johnnyhuy/s2000-digital-dash/docs/assets/compare/compare_ap2_caution.png

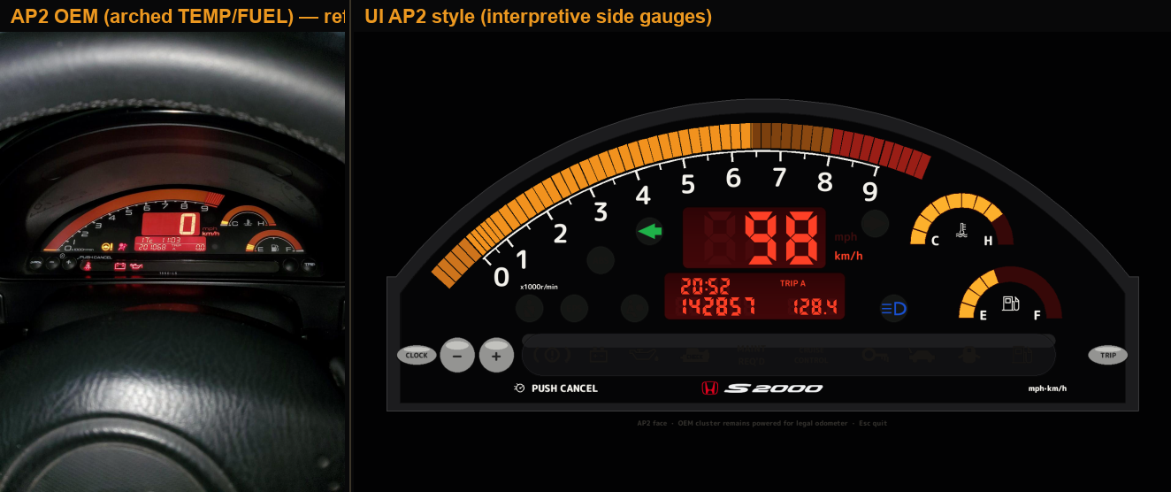
docs/assets/compare/compare_ap2_caution.png
