johnnyhuy/s2000-digital-dash/docs/assets/web-ap1-dark.png

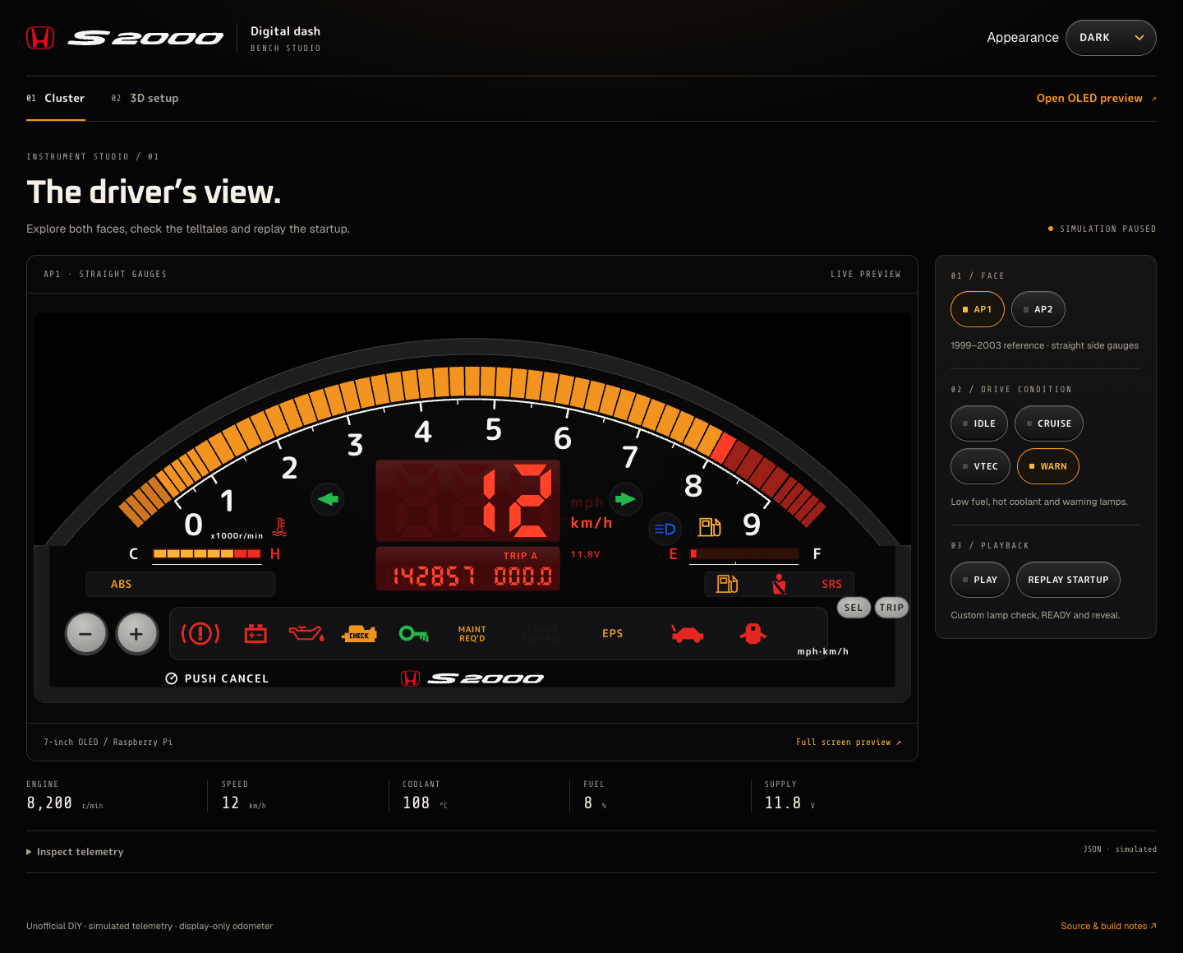
docs/assets/web-ap1-dark.png
