johnnyhuy/s2000-digital-dash/docs/assets/web-ap1-light.png

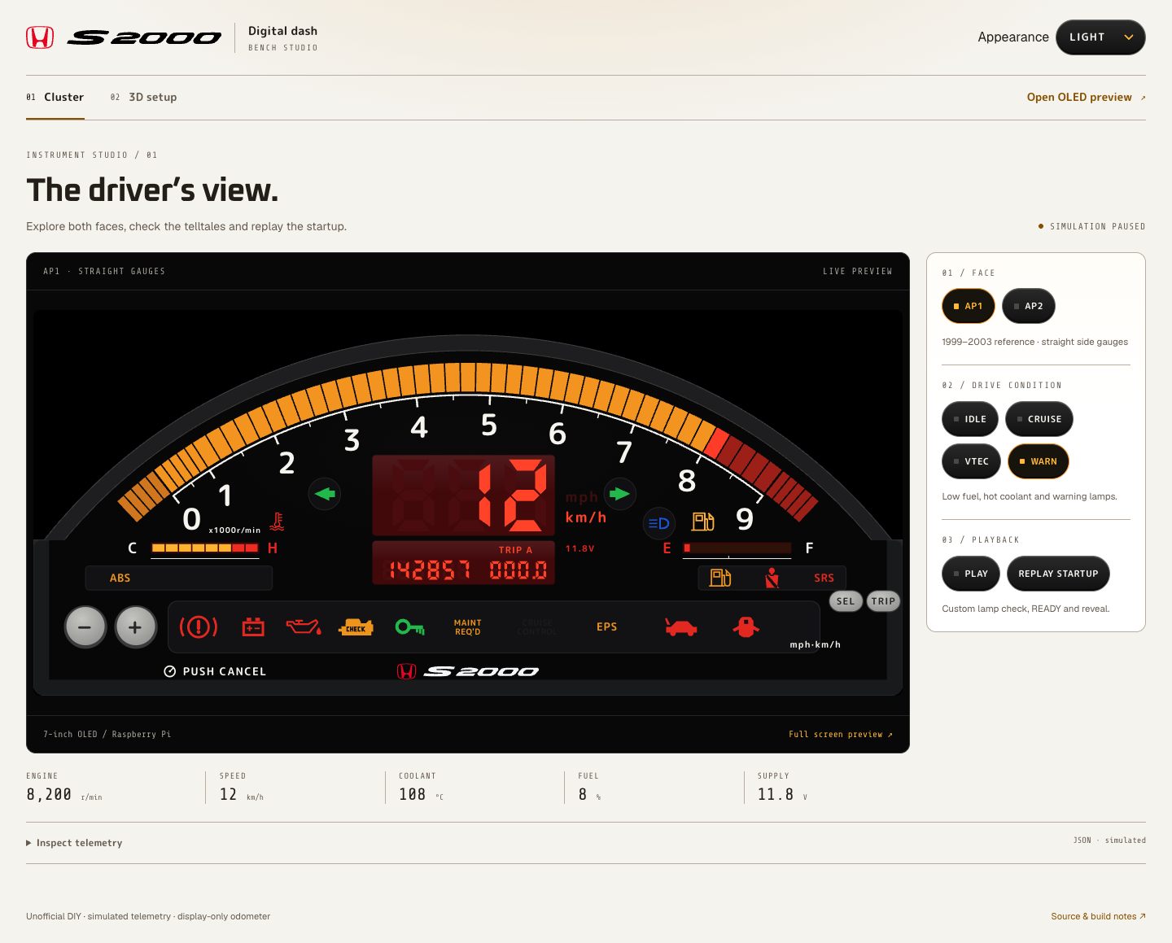
docs/assets/web-ap1-light.png
