johnnyhuy/s2000-digital-dash/docs/assets/web-ap2-warn.png

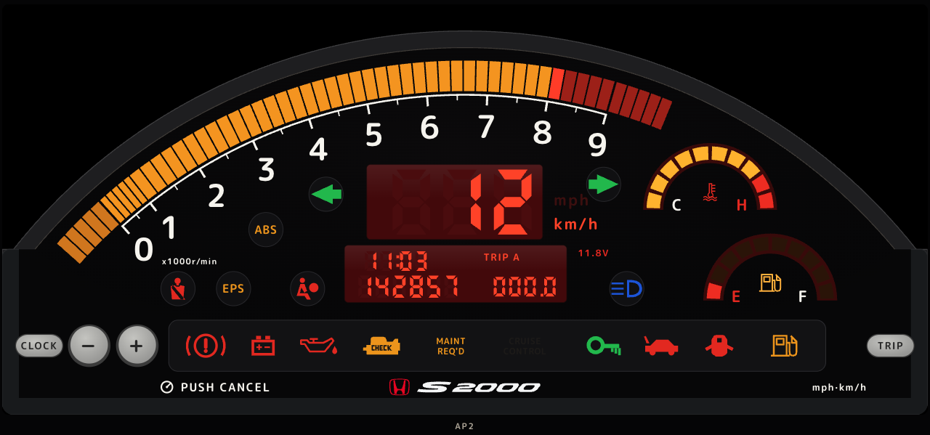
docs/assets/web-ap2-warn.png
