johnnyhuy/s2000-digital-dash/shots/harness/harness_ap2_live.png

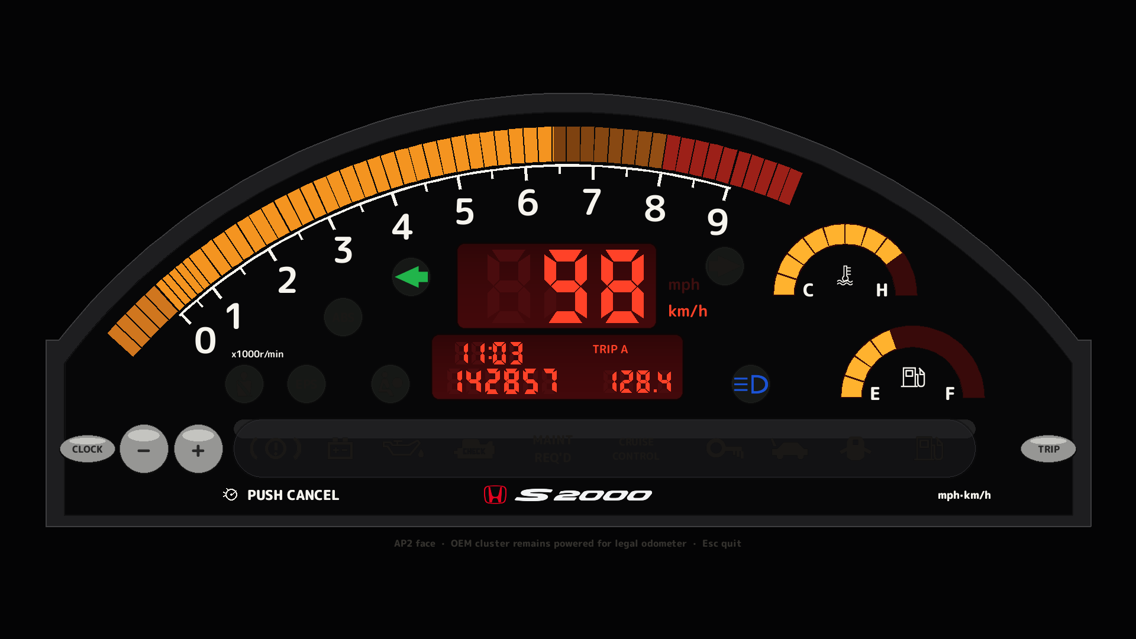
shots/harness/harness_ap2_live.png
