johnnyhuy/s2000-digital-dash/cad/replace_face/face_lock.scad

// AP1 face lock — generated by src/face_spec.py. Do not edit; edit the spec.
style = "ap1";
module_aspect = 2.35;
tach_cx = 0.5;
tach_cy_h = 1.487;
tach_r_out = 0.59;
tach_r_in = 0.5569999999999999;
tach_r_line = 0.5529999999999999;
tach_r_num = 0.5189999999999999;
tach_num_size = 0.034;
tach_a0 = -127.8;
tach_a9 = -52.2;
tach_hatch_deg = 5.5;
crown_cy_h = 1.487;
crown_r = 0.604;
crown_lip = 0.018;
spring_y_h = 0.58;
speed_win = [0.39, 0.35, 0.21, 0.218];
odo_win = [0.39, 0.582, 0.21, 0.118];
temp_win = [0.135, 0.586, 0.125, 0.03];
temp_icon = [0.28, 0.53];
temp_c = [0.115, 0.601];
temp_h = [0.276, 0.601];
temp_underline_y = 0.63;
fuel_win = [0.747, 0.586, 0.125, 0.03];
fuel_icon = [0.77, 0.53];
fuel_e = [0.73, 0.601];
fuel_f = [0.894, 0.601];
fuel_underline_y = 0.63;
side_gauges_arched = false;
arc_lamps = [[0.335, 0.455, 0.016], [0.675, 0.455, 0.016], [0.72, 0.535, 0.014]];
arc_lamp_r = 0.0185;
strip = [0.155, 0.745, 0.75, 0.14];
strip_lamps = [[0.19, 0.815, 0.03], [0.253, 0.815, 0.022], [0.311, 0.815, 0.024], [0.371, 0.815, 0.024], [0.433, 0.815, 0.02], [0.5, 0.815, 0.02], [0.58, 0.815, 0.016], [0.66, 0.815, 0.02], [0.745, 0.815, 0.022], [0.82, 0.815, 0.024]];
panel_left = [0.06, 0.65, 0.215, 0.065];
panel_right = [0.765, 0.65, 0.17, 0.065];
btn_minus = [0.06, 0.815];
btn_plus = [0.118, 0.815];
btn_d = 0.05;
btn_sel = [0.935, 0.745];
btn_trip = [0.978, 0.745];
oval_w = 0.04;
oval_h = 0.06;
cancel_icon = [0.157, 0.935];
cancel_text = [0.172, 0.935];
units_label = [0.9, 0.862];
