johnnyhuy/s2000-digital-dash/cad/replace_face/rubber_buttons.scad

// =============================================================================
// PLACEHOLDER — rubber buttons (Option 1 replace-face)
// =============================================================================
// −/+ PUSH CANCEL rocker, SEL oval, TRIP oval.
// Zones follow refs/flat/DIMENSIONS.md percentages. Callipers UNKNOWN.
// NOT OEM rubber and NOT a verified AP1 drop-in.
//
// F5 plate preview only. Export button_rocker / button_sel / button_trip
// as separate solids (one solid per STL).
//
// Print in TPU 95A, or print a master and cast silicone.
// Do NOT use PLA. Cabin-facing hard parts around these stay PETG / ASA.
// =============================================================================

include <parts.scad>
rubber_buttons_print();
