johnnyhuy/s2000-digital-dash/docs/assets/setup-assembled.png

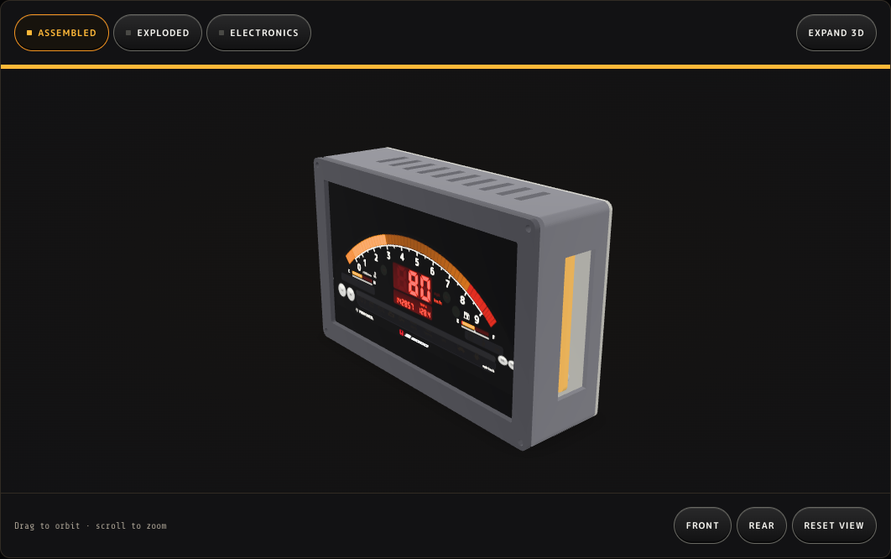
docs/assets/setup-assembled.png
