johnnyhuy/s2000-digital-dash/docs/assets/web-setup-light.png

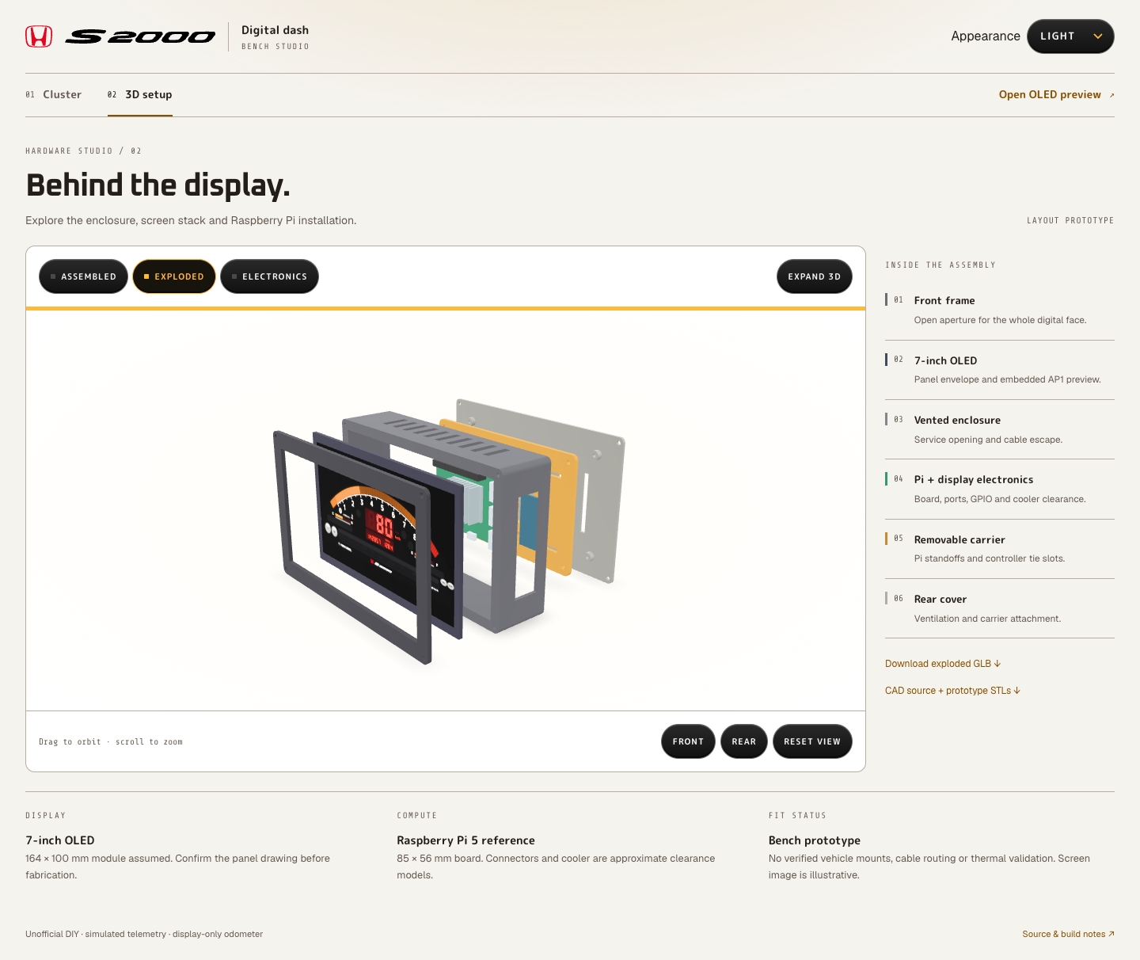
docs/assets/web-setup-light.png
